mnarigon/backplane/backplane.kicad_sch

## KiCad design backplane.kicad_sch (2023-11-16)

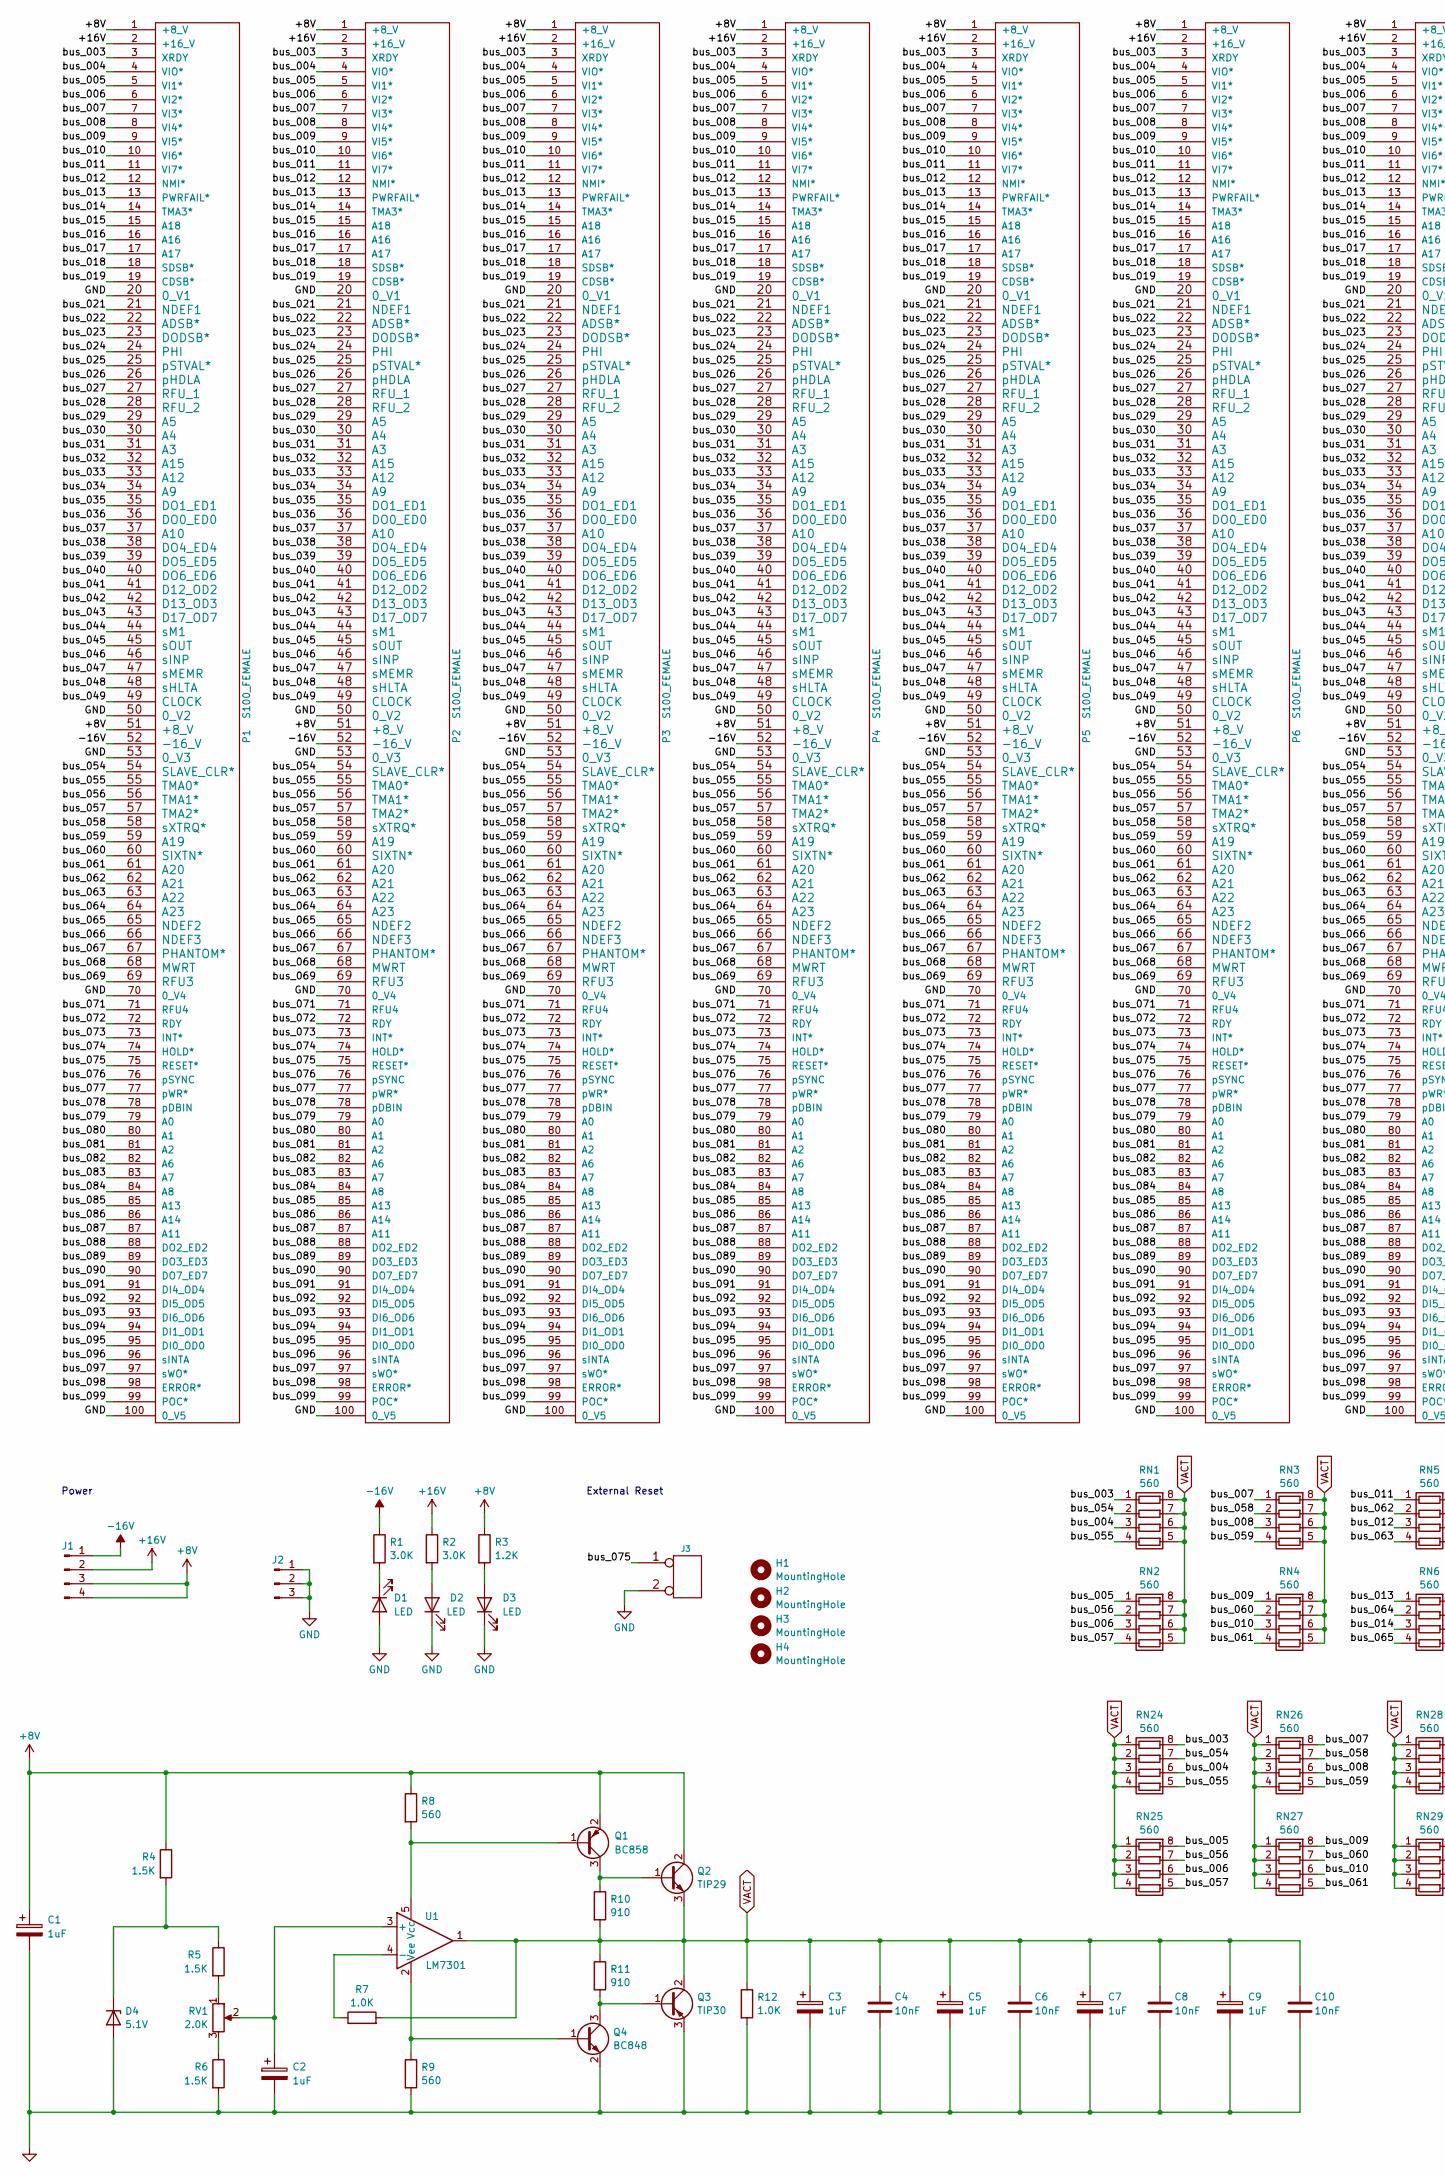
[picture p17: schematic backplane.kicad_sch, part in row 1, column 1]

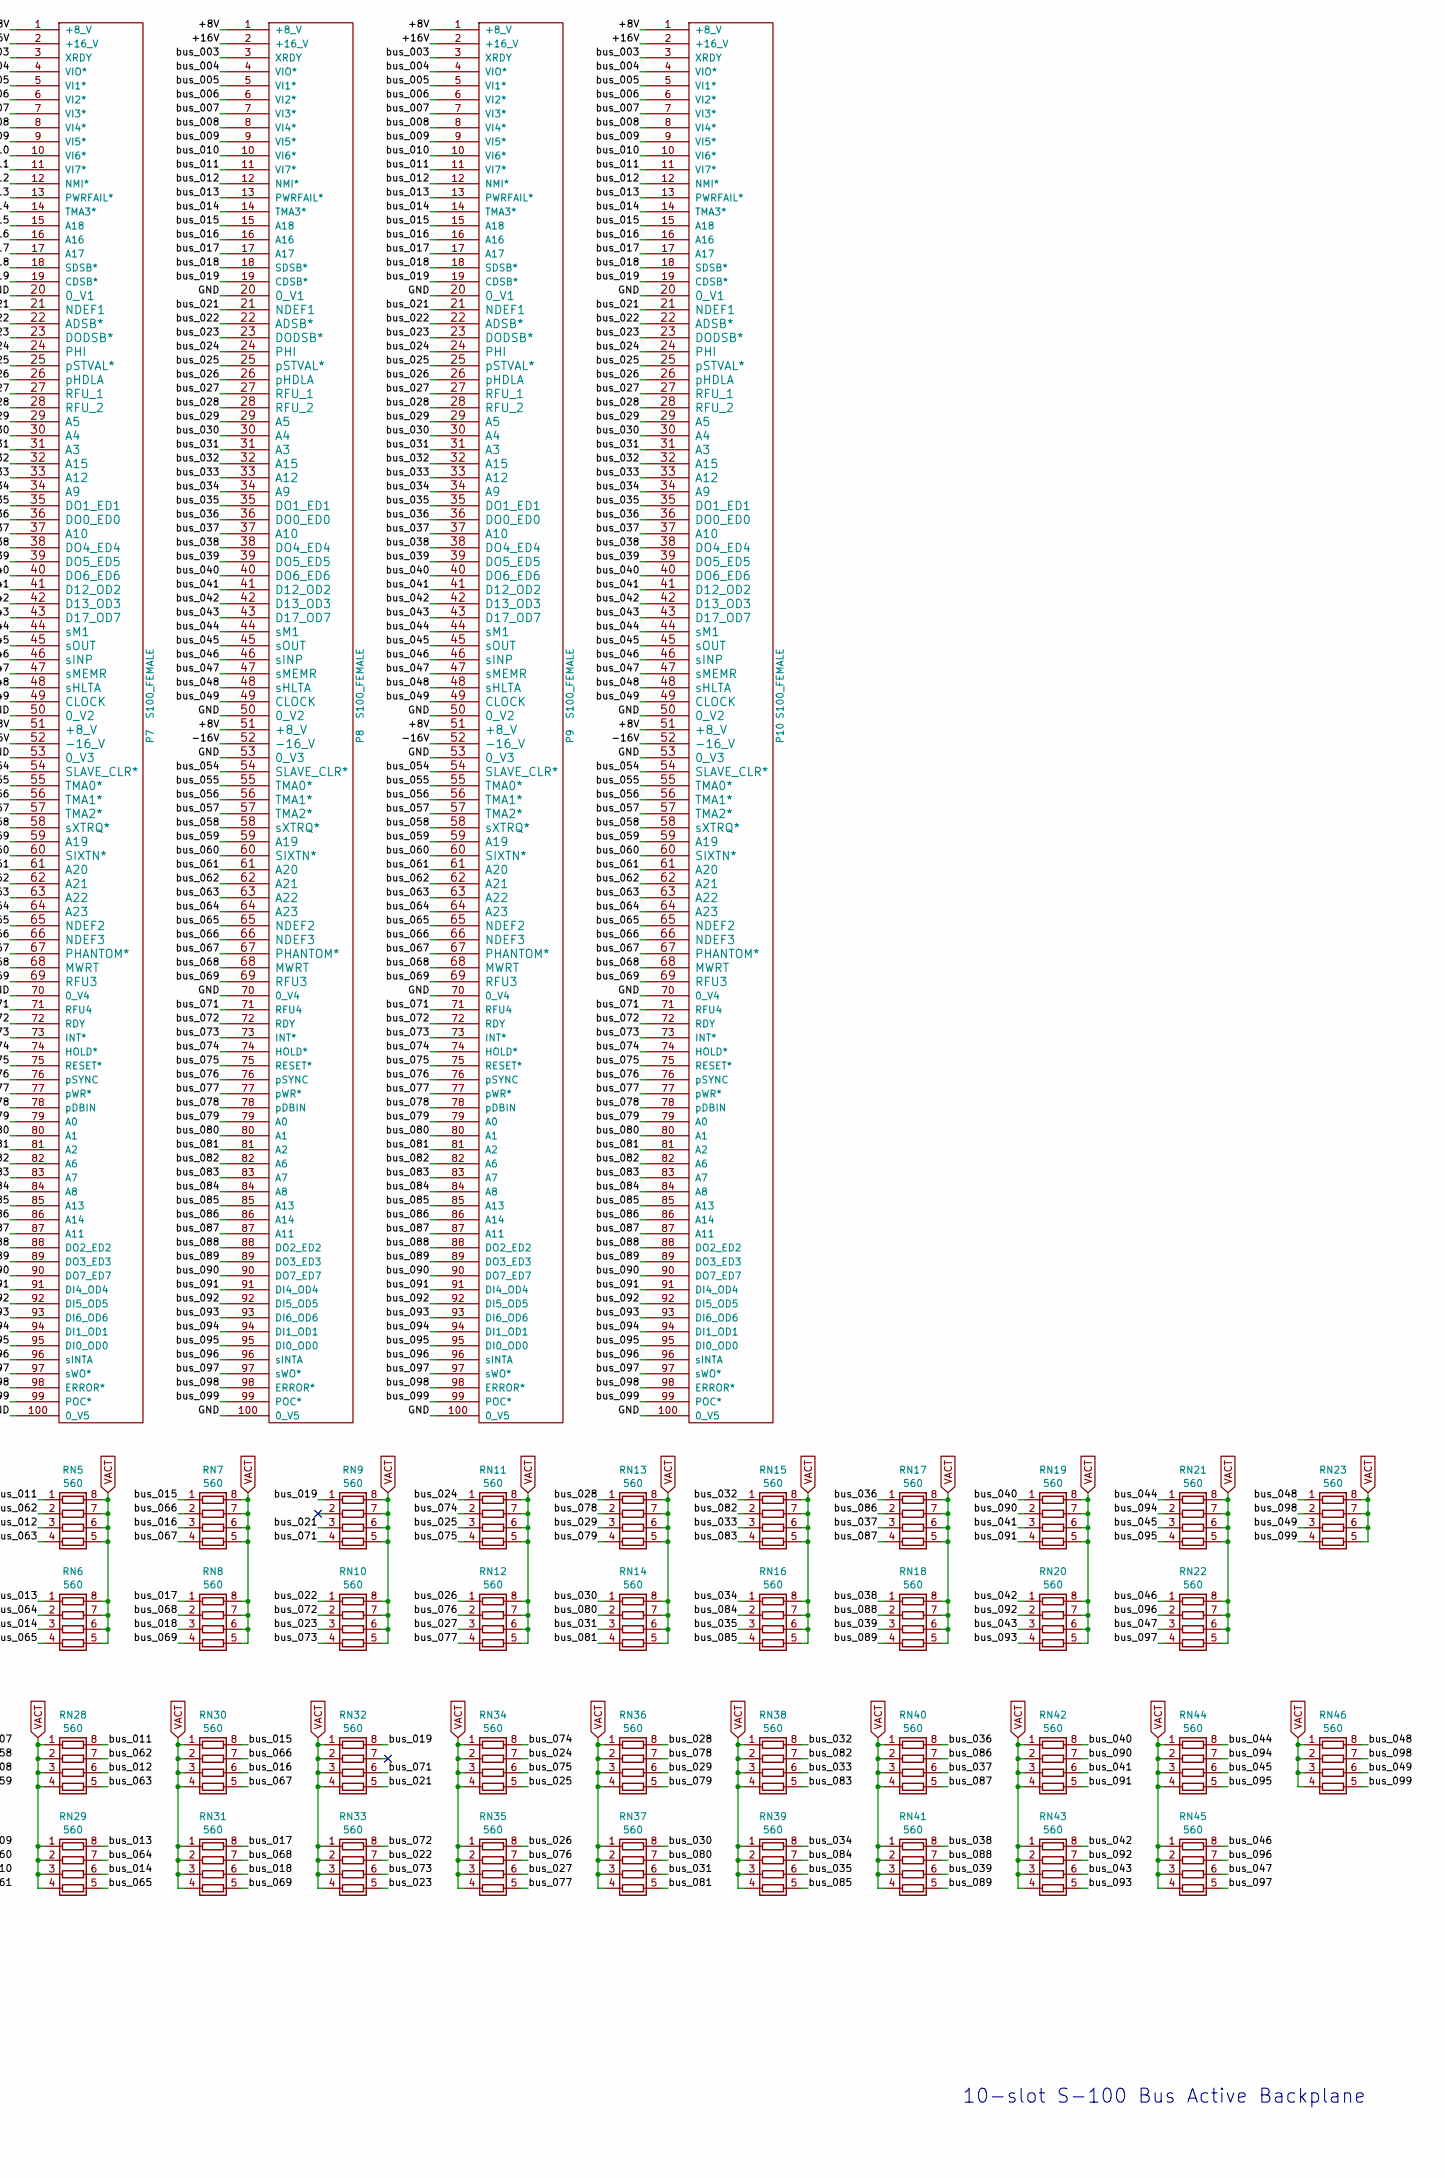
[picture p18: schematic backplane.kicad_sch, part in row 1, column 2]

Parts:
C1, C2, C3, C5, C7, C9: 1uF; CP_0805
C4, C6, C8, C10: 10nF; C_0805
D1, D2, D3: LED; LED_0805
D4: 5.1V; D_SOD-323
H1, H2, H3, H4: MountingHole; Mounting_Hole_6-32
J1: AMP_640445-4
J2: AMP_640445-3
J3: CONN_2; AMP_640454-2
P1, P2, P3, P4, P5, P6, P7, P8, P9, P10: S100_FEMALE; EDAC_346-100-520-202
Q1: BC858; SOT-23-3
Q2: TIP29; TO-220-3_Horizontal
Q3: TIP30; TO-220-3_Horizontal
Q4: BC848; SOT-23-3
R1, R2: 3.0K; R_0805
R3: 1.2K; R_0805
R4, R5, R6: 1.5K; R_0805
R7, R12: 1.0K; R_0805
R8, R9: 560; R_0805
R10, R11: 910; R_0805
RN1, RN2, RN3, RN4, RN5, RN6, RN7, RN8, RN9, RN10, RN11, RN12, RN13, RN14, RN15, RN16, RN17, RN18, RN19, RN20, RN21, RN22, RN23, RN24, RN25, RN26, RN27, RN28, RN29, RN30, RN31, RN32, RN33, RN34, RN35, RN36, RN37, RN38, RN39, RN40, RN41, RN42, RN43, RN44, RN45, RN46: 560; R_Array_Convex_4x1206
RV1: 2.0K; Potentiometer_Bourns_TC33X
U1: LM7301; SOT-23-5

Connections:
+8V: C1.1, J1.3, J1.4, P1.1 (+8_V), P1.51 (+8_V), P2.1 (+8_V), P2.51 (+8_V), P3.1 (+8_V), P3.51 (+8_V), P4.1 (+8_V), P4.51 (+8_V), P5.1 (+8_V), P5.51 (+8_V), P6.1 (+8_V), P6.51 (+8_V), P7.1 (+8_V), P7.51 (+8_V), P8.1 (+8_V), P8.51 (+8_V), P9.1 (+8_V), P9.51 (+8_V), P10.1 (+8_V), P10.51 (+8_V), Q1.2 (E), Q2.2 (C), R3.1, R4.1, R8.1
+16V: J1.2, P1.2 (+16_V), P2.2 (+16_V), P3.2 (+16_V), P4.2 (+16_V), P5.2 (+16_V), P6.2 (+16_V), P7.2 (+16_V), P8.2 (+16_V), P9.2 (+16_V), P10.2 (+16_V), R2.1
-16V: J1.1, P1.52 (-16_V), P2.52 (-16_V), P3.52 (-16_V), P4.52 (-16_V), P5.52 (-16_V), P6.52 (-16_V), P7.52 (-16_V), P8.52 (-16_V), P9.52 (-16_V), P10.52 (-16_V), R1.1
GND: C1.2, C2.2, C3.2, C4.2, C5.2, C6.2, C7.2, C8.2, C9.2, C10.2, D1.2 (A), D2.1 (K), D3.1 (K), D4.2 (A), J2.1, J2.2, J2.3, J3.2 (PM), P1.20 (0_V1), P1.50 (0_V2), P1.53 (0_V3), P1.70 (0_V4), P1.100 (0_V5), P2.20 (0_V1), P2.50 (0_V2), P2.53 (0_V3), P2.70 (0_V4), P2.100 (0_V5), P3.20 (0_V1), P3.50 (0_V2), P3.53 (0_V3), P3.70 (0_V4), P3.100 (0_V5), P4.20 (0_V1), P4.50 (0_V2), P4.53 (0_V3), P4.70 (0_V4), P4.100 (0_V5), P5.20 (0_V1), P5.50 (0_V2), P5.53 (0_V3), P5.70 (0_V4), P5.100 (0_V5), P6.20 (0_V1), P6.50 (0_V2), P6.53 (0_V3), P6.70 (0_V4), P6.100 (0_V5), P7.20 (0_V1), P7.50 (0_V2), P7.53 (0_V3), P7.70 (0_V4), P7.100 (0_V5), P8.20 (0_V1), P8.50 (0_V2), P8.53 (0_V3), P8.70 (0_V4), P8.100 (0_V5), P9.20 (0_V1), P9.50 (0_V2), P9.53 (0_V3), P9.70 (0_V4), P9.100 (0_V5), P10.20 (0_V1), P10.50 (0_V2), P10.53 (0_V3), P10.70 (0_V4), P10.100 (0_V5), Q3.3 (E), Q4.2 (E), R6.2, R9.2, R12.2
unnamed: C2.1, RV1.2, U1.3 (+)
unnamed: D1.1 (K), R1.2
unnamed: D2.2 (A), R2.2
unnamed: D3.2 (A), R3.2
unnamed: D4.1 (K), R4.2, R5.1
unnamed: Q1.1 (B), R8.2, U1.5 (Vcc)
unnamed: Q1.3 (C), Q2.1 (B), R10.1
unnamed: Q3.1 (B), Q4.3 (C), R11.2
unnamed: Q4.1 (B), R9.1, U1.2 (Vee)
unnamed: R5.2, RV1.1
unnamed: R6.1, RV1.3
unnamed: R7.1, U1.4 (-)
VACT: C3.1, C4.1, C5.1, C6.1, C7.1, C8.1, C9.1, C10.1, Q2.3 (E), Q3.2 (C), R7.2, R10.2, R11.1, R12.1, RN1.5 (R4.2), RN1.6 (R3.2), RN1.7 (R2.2), RN1.8 (R1.2), RN2.5 (R4.2), RN2.6 (R3.2), RN2.7 (R2.2), RN2.8 (R1.2), RN3.5 (R4.2), RN3.6 (R3.2), RN3.7 (R2.2), RN3.8 (R1.2), RN4.5 (R4.2), RN4.6 (R3.2), RN4.7 (R2.2), RN4.8 (R1.2), RN5.5 (R4.2), RN5.6 (R3.2), RN5.7 (R2.2), RN5.8 (R1.2), RN6.5 (R4.2), RN6.6 (R3.2), RN6.7 (R2.2), RN6.8 (R1.2), RN7.5 (R4.2), RN7.6 (R3.2), RN7.7 (R2.2), RN7.8 (R1.2), RN8.5 (R4.2), RN8.6 (R3.2), RN8.7 (R2.2), RN8.8 (R1.2), RN9.5 (R4.2), RN9.6 (R3.2), RN9.7 (R2.2), RN9.8 (R1.2), RN10.5 (R4.2), RN10.6 (R3.2), RN10.7 (R2.2), RN10.8 (R1.2), RN11.5 (R4.2), RN11.6 (R3.2), RN11.7 (R2.2), RN11.8 (R1.2), RN12.5 (R4.2), RN12.6 (R3.2), RN12.7 (R2.2), RN12.8 (R1.2), RN13.5 (R4.2), RN13.6 (R3.2), RN13.7 (R2.2), RN13.8 (R1.2), RN14.5 (R4.2), RN14.6 (R3.2), RN14.7 (R2.2), RN14.8 (R1.2), RN15.5 (R4.2), RN15.6 (R3.2), RN15.7 (R2.2), RN15.8 (R1.2), RN16.5 (R4.2), RN16.6 (R3.2), RN16.7 (R2.2), RN16.8 (R1.2), RN17.5 (R4.2), RN17.6 (R3.2), RN17.7 (R2.2), RN17.8 (R1.2), RN18.5 (R4.2), RN18.6 (R3.2), RN18.7 (R2.2), RN18.8 (R1.2), RN19.5 (R4.2), RN19.6 (R3.2), RN19.7 (R2.2), RN19.8 (R1.2), RN20.5 (R4.2), RN20.6 (R3.2), RN20.7 (R2.2), RN20.8 (R1.2), RN21.5 (R4.2), RN21.6 (R3.2), RN21.7 (R2.2), RN21.8 (R1.2), RN22.5 (R4.2), RN22.6 (R3.2), RN22.7 (R2.2), RN22.8 (R1.2), RN23.5 (R4.2), RN23.6 (R3.2), RN23.7 (R2.2), RN23.8 (R1.2), RN24.1 (R1.1), RN24.2 (R2.1), RN24.3 (R3.1), RN24.4 (R4.1), RN25.1 (R1.1), RN25.2 (R2.1), RN25.3 (R3.1), RN25.4 (R4.1), RN26.1 (R1.1), RN26.2 (R2.1), RN26.3 (R3.1), RN26.4 (R4.1), RN27.1 (R1.1), RN27.2 (R2.1), RN27.3 (R3.1), RN27.4 (R4.1), RN28.1 (R1.1), RN28.2 (R2.1), RN28.3 (R3.1), RN28.4 (R4.1), RN29.1 (R1.1), RN29.2 (R2.1), RN29.3 (R3.1), RN29.4 (R4.1), RN30.1 (R1.1), RN30.2 (R2.1), RN30.3 (R3.1), RN30.4 (R4.1), RN31.1 (R1.1), RN31.2 (R2.1), RN31.3 (R3.1), RN31.4 (R4.1), RN32.1 (R1.1), RN32.2 (R2.1), RN32.3 (R3.1), RN32.4 (R4.1), RN33.1 (R1.1), RN33.2 (R2.1), RN33.3 (R3.1), RN33.4 (R4.1), RN34.1 (R1.1), RN34.2 (R2.1), RN34.3 (R3.1), RN34.4 (R4.1), RN35.1 (R1.1), RN35.2 (R2.1), RN35.3 (R3.1), RN35.4 (R4.1), RN36.1 (R1.1), RN36.2 (R2.1), RN36.3 (R3.1), RN36.4 (R4.1), RN37.1 (R1.1), RN37.2 (R2.1), RN37.3 (R3.1), RN37.4 (R4.1), RN38.1 (R1.1), RN38.2 (R2.1), RN38.3 (R3.1), RN38.4 (R4.1), RN39.1 (R1.1), RN39.2 (R2.1), RN39.3 (R3.1), RN39.4 (R4.1), RN40.1 (R1.1), RN40.2 (R2.1), RN40.3 (R3.1), RN40.4 (R4.1), RN41.1 (R1.1), RN41.2 (R2.1), RN41.3 (R3.1), RN41.4 (R4.1), RN42.1 (R1.1), RN42.2 (R2.1), RN42.3 (R3.1), RN42.4 (R4.1), RN43.1 (R1.1), RN43.2 (R2.1), RN43.3 (R3.1), RN43.4 (R4.1), RN44.1 (R1.1), RN44.2 (R2.1), RN44.3 (R3.1), RN44.4 (R4.1), RN45.1 (R1.1), RN45.2 (R2.1), RN45.3 (R3.1), RN45.4 (R4.1), RN46.1 (R1.1), RN46.2 (R2.1), RN46.3 (R3.1), RN46.4 (R4.1), U1.1
bus_003: P1.3 (XRDY), P2.3 (XRDY), P3.3 (XRDY), P4.3 (XRDY), P5.3 (XRDY), P6.3 (XRDY), P7.3 (XRDY), P8.3 (XRDY), P9.3 (XRDY), P10.3 (XRDY), RN1.1 (R1.1), RN24.8 (R1.2)
bus_004: P1.4 (VIO*), P2.4 (VIO*), P3.4 (VIO*), P4.4 (VIO*), P5.4 (VIO*), P6.4 (VIO*), P7.4 (VIO*), P8.4 (VIO*), P9.4 (VIO*), P10.4 (VIO*), RN1.3 (R3.1), RN24.6 (R3.2)
bus_005: P1.5 (VI1*), P2.5 (VI1*), P3.5 (VI1*), P4.5 (VI1*), P5.5 (VI1*), P6.5 (VI1*), P7.5 (VI1*), P8.5 (VI1*), P9.5 (VI1*), P10.5 (VI1*), RN2.1 (R1.1), RN25.8 (R1.2)
bus_006: P1.6 (VI2*), P2.6 (VI2*), P3.6 (VI2*), P4.6 (VI2*), P5.6 (VI2*), P6.6 (VI2*), P7.6 (VI2*), P8.6 (VI2*), P9.6 (VI2*), P10.6 (VI2*), RN2.3 (R3.1), RN25.6 (R3.2)
bus_007: P1.7 (VI3*), P2.7 (VI3*), P3.7 (VI3*), P4.7 (VI3*), P5.7 (VI3*), P6.7 (VI3*), P7.7 (VI3*), P8.7 (VI3*), P9.7 (VI3*), P10.7 (VI3*), RN3.1 (R1.1), RN26.8 (R1.2)
bus_008: P1.8 (VI4*), P2.8 (VI4*), P3.8 (VI4*), P4.8 (VI4*), P5.8 (VI4*), P6.8 (VI4*), P7.8 (VI4*), P8.8 (VI4*), P9.8 (VI4*), P10.8 (VI4*), RN3.3 (R3.1), RN26.6 (R3.2)
bus_009: P1.9 (VI5*), P2.9 (VI5*), P3.9 (VI5*), P4.9 (VI5*), P5.9 (VI5*), P6.9 (VI5*), P7.9 (VI5*), P8.9 (VI5*), P9.9 (VI5*), P10.9 (VI5*), RN4.1 (R1.1), RN27.8 (R1.2)
bus_010: P1.10 (VI6*), P2.10 (VI6*), P3.10 (VI6*), P4.10 (VI6*), P5.10 (VI6*), P6.10 (VI6*), P7.10 (VI6*), P8.10 (VI6*), P9.10 (VI6*), P10.10 (VI6*), RN4.3 (R3.1), RN27.6 (R3.2)
bus_011: P1.11 (VI7*), P2.11 (VI7*), P3.11 (VI7*), P4.11 (VI7*), P5.11 (VI7*), P6.11 (VI7*), P7.11 (VI7*), P8.11 (VI7*), P9.11 (VI7*), P10.11 (VI7*), RN5.1 (R1.1), RN28.8 (R1.2)
bus_012: P1.12 (NMI*), P2.12 (NMI*), P3.12 (NMI*), P4.12 (NMI*), P5.12 (NMI*), P6.12 (NMI*), P7.12 (NMI*), P8.12 (NMI*), P9.12 (NMI*), P10.12 (NMI*), RN5.3 (R3.1), RN28.6 (R3.2)
bus_013: P1.13 (PWRFAIL*), P2.13 (PWRFAIL*), P3.13 (PWRFAIL*), P4.13 (PWRFAIL*), P5.13 (PWRFAIL*), P6.13 (PWRFAIL*), P7.13 (PWRFAIL*), P8.13 (PWRFAIL*), P9.13 (PWRFAIL*), P10.13 (PWRFAIL*), RN6.1 (R1.1), RN29.8 (R1.2)
bus_014: P1.14 (TMA3*), P2.14 (TMA3*), P3.14 (TMA3*), P4.14 (TMA3*), P5.14 (TMA3*), P6.14 (TMA3*), P7.14 (TMA3*), P8.14 (TMA3*), P9.14 (TMA3*), P10.14 (TMA3*), RN6.3 (R3.1), RN29.6 (R3.2)
bus_015: P1.15 (A18), P2.15 (A18), P3.15 (A18), P4.15 (A18), P5.15 (A18), P6.15 (A18), P7.15 (A18), P8.15 (A18), P9.15 (A18), P10.15 (A18), RN7.1 (R1.1), RN30.8 (R1.2)
bus_016: P1.16 (A16), P2.16 (A16), P3.16 (A16), P4.16 (A16), P5.16 (A16), P6.16 (A16), P7.16 (A16), P8.16 (A16), P9.16 (A16), P10.16 (A16), RN7.3 (R3.1), RN30.6 (R3.2)
bus_017: P1.17 (A17), P2.17 (A17), P3.17 (A17), P4.17 (A17), P5.17 (A17), P6.17 (A17), P7.17 (A17), P8.17 (A17), P9.17 (A17), P10.17 (A17), RN8.1 (R1.1), RN31.8 (R1.2)
bus_018: P1.18 (SDSB*), P2.18 (SDSB*), P3.18 (SDSB*), P4.18 (SDSB*), P5.18 (SDSB*), P6.18 (SDSB*), P7.18 (SDSB*), P8.18 (SDSB*), P9.18 (SDSB*), P10.18 (SDSB*), RN8.3 (R3.1), RN31.6 (R3.2)
bus_019: P1.19 (CDSB*), P2.19 (CDSB*), P3.19 (CDSB*), P4.19 (CDSB*), P5.19 (CDSB*), P6.19 (CDSB*), P7.19 (CDSB*), P8.19 (CDSB*), P9.19 (CDSB*), P10.19 (CDSB*), RN9.1 (R1.1), RN32.8 (R1.2)
bus_021: P1.21 (NDEF1), P2.21 (NDEF1), P3.21 (NDEF1), P4.21 (NDEF1), P5.21 (NDEF1), P6.21 (NDEF1), P7.21 (NDEF1), P8.21 (NDEF1), P9.21 (NDEF1), P10.21 (NDEF1), RN9.3 (R3.1), RN32.5 (R4.2)
bus_022: P1.22 (ADSB*), P2.22 (ADSB*), P3.22 (ADSB*), P4.22 (ADSB*), P5.22 (ADSB*), P6.22 (ADSB*), P7.22 (ADSB*), P8.22 (ADSB*), P9.22 (ADSB*), P10.22 (ADSB*), RN10.1 (R1.1), RN33.7 (R2.2)
bus_023: P1.23 (DODSB*), P2.23 (DODSB*), P3.23 (DODSB*), P4.23 (DODSB*), P5.23 (DODSB*), P6.23 (DODSB*), P7.23 (DODSB*), P8.23 (DODSB*), P9.23 (DODSB*), P10.23 (DODSB*), RN10.3 (R3.1), RN33.5 (R4.2)
bus_024: P1.24 (PHI), P2.24 (PHI), P3.24 (PHI), P4.24 (PHI), P5.24 (PHI), P6.24 (PHI), P7.24 (PHI), P8.24 (PHI), P9.24 (PHI), P10.24 (PHI), RN11.1 (R1.1), RN34.7 (R2.2)
bus_025: P1.25 (pSTVAL*), P2.25 (pSTVAL*), P3.25 (pSTVAL*), P4.25 (pSTVAL*), P5.25 (pSTVAL*), P6.25 (pSTVAL*), P7.25 (pSTVAL*), P8.25 (pSTVAL*), P9.25 (pSTVAL*), P10.25 (pSTVAL*), RN11.3 (R3.1), RN34.5 (R4.2)
bus_026: P1.26 (pHDLA), P2.26 (pHDLA), P3.26 (pHDLA), P4.26 (pHDLA), P5.26 (pHDLA), P6.26 (pHDLA), P7.26 (pHDLA), P8.26 (pHDLA), P9.26 (pHDLA), P10.26 (pHDLA), RN12.1 (R1.1), RN35.8 (R1.2)
bus_027: P1.27 (RFU_1), P2.27 (RFU_1), P3.27 (RFU_1), P4.27 (RFU_1), P5.27 (RFU_1), P6.27 (RFU_1), P7.27 (RFU_1), P8.27 (RFU_1), P9.27 (RFU_1), P10.27 (RFU_1), RN12.3 (R3.1), RN35.6 (R3.2)
bus_028: P1.28 (RFU_2), P2.28 (RFU_2), P3.28 (RFU_2), P4.28 (RFU_2), P5.28 (RFU_2), P6.28 (RFU_2), P7.28 (RFU_2), P8.28 (RFU_2), P9.28 (RFU_2), P10.28 (RFU_2), RN13.1 (R1.1), RN36.8 (R1.2)
bus_029: P1.29 (A5), P2.29 (A5), P3.29 (A5), P4.29 (A5), P5.29 (A5), P6.29 (A5), P7.29 (A5), P8.29 (A5), P9.29 (A5), P10.29 (A5), RN13.3 (R3.1), RN36.6 (R3.2)
bus_030: P1.30 (A4), P2.30 (A4), P3.30 (A4), P4.30 (A4), P5.30 (A4), P6.30 (A4), P7.30 (A4), P8.30 (A4), P9.30 (A4), P10.30 (A4), RN14.1 (R1.1), RN37.8 (R1.2)
bus_031: P1.31 (A3), P2.31 (A3), P3.31 (A3), P4.31 (A3), P5.31 (A3), P6.31 (A3), P7.31 (A3), P8.31 (A3), P9.31 (A3), P10.31 (A3), RN14.3 (R3.1), RN37.6 (R3.2)
bus_032: P1.32 (A15), P2.32 (A15), P3.32 (A15), P4.32 (A15), P5.32 (A15), P6.32 (A15), P7.32 (A15), P8.32 (A15), P9.32 (A15), P10.32 (A15), RN15.1 (R1.1), RN38.8 (R1.2)
bus_033: P1.33 (A12), P2.33 (A12), P3.33 (A12), P4.33 (A12), P5.33 (A12), P6.33 (A12), P7.33 (A12), P8.33 (A12), P9.33 (A12), P10.33 (A12), RN15.3 (R3.1), RN38.6 (R3.2)
bus_034: P1.34 (A9), P2.34 (A9), P3.34 (A9), P4.34 (A9), P5.34 (A9), P6.34 (A9), P7.34 (A9), P8.34 (A9), P9.34 (A9), P10.34 (A9), RN16.1 (R1.1), RN39.8 (R1.2)
bus_035: P1.35 (DO1_ED1), P2.35 (DO1_ED1), P3.35 (DO1_ED1), P4.35 (DO1_ED1), P5.35 (DO1_ED1), P6.35 (DO1_ED1), P7.35 (DO1_ED1), P8.35 (DO1_ED1), P9.35 (DO1_ED1), P10.35 (DO1_ED1), RN16.3 (R3.1), RN39.6 (R3.2)
bus_036: P1.36 (DO0_ED0), P2.36 (DO0_ED0), P3.36 (DO0_ED0), P4.36 (DO0_ED0), P5.36 (DO0_ED0), P6.36 (DO0_ED0), P7.36 (DO0_ED0), P8.36 (DO0_ED0), P9.36 (DO0_ED0), P10.36 (DO0_ED0), RN17.1 (R1.1), RN40.8 (R1.2)
bus_037: P1.37 (A10), P2.37 (A10), P3.37 (A10), P4.37 (A10), P5.37 (A10), P6.37 (A10), P7.37 (A10), P8.37 (A10), P9.37 (A10), P10.37 (A10), RN17.3 (R3.1), RN40.6 (R3.2)
bus_038: P1.38 (DO4_ED4), P2.38 (DO4_ED4), P3.38 (DO4_ED4), P4.38 (DO4_ED4), P5.38 (DO4_ED4), P6.38 (DO4_ED4), P7.38 (DO4_ED4), P8.38 (DO4_ED4), P9.38 (DO4_ED4), P10.38 (DO4_ED4), RN18.1 (R1.1), RN41.8 (R1.2)
bus_039: P1.39 (DO5_ED5), P2.39 (DO5_ED5), P3.39 (DO5_ED5), P4.39 (DO5_ED5), P5.39 (DO5_ED5), P6.39 (DO5_ED5), P7.39 (DO5_ED5), P8.39 (DO5_ED5), P9.39 (DO5_ED5), P10.39 (DO5_ED5), RN18.3 (R3.1), RN41.6 (R3.2)
bus_040: P1.40 (DO6_ED6), P2.40 (DO6_ED6), P3.40 (DO6_ED6), P4.40 (DO6_ED6), P5.40 (DO6_ED6), P6.40 (DO6_ED6), P7.40 (DO6_ED6), P8.40 (DO6_ED6), P9.40 (DO6_ED6), P10.40 (DO6_ED6), RN19.1 (R1.1), RN42.8 (R1.2)
bus_041: P1.41 (D12_OD2), P2.41 (D12_OD2), P3.41 (D12_OD2), P4.41 (D12_OD2), P5.41 (D12_OD2), P6.41 (D12_OD2), P7.41 (D12_OD2), P8.41 (D12_OD2), P9.41 (D12_OD2), P10.41 (D12_OD2), RN19.3 (R3.1), RN42.6 (R3.2)
bus_042: P1.42 (D13_OD3), P2.42 (D13_OD3), P3.42 (D13_OD3), P4.42 (D13_OD3), P5.42 (D13_OD3), P6.42 (D13_OD3), P7.42 (D13_OD3), P8.42 (D13_OD3), P9.42 (D13_OD3), P10.42 (D13_OD3), RN20.1 (R1.1), RN43.8 (R1.2)
bus_043: P1.43 (D17_OD7), P2.43 (D17_OD7), P3.43 (D17_OD7), P4.43 (D17_OD7), P5.43 (D17_OD7), P6.43 (D17_OD7), P7.43 (D17_OD7), P8.43 (D17_OD7), P9.43 (D17_OD7), P10.43 (D17_OD7), RN20.3 (R3.1), RN43.6 (R3.2)
bus_044: P1.44 (sM1), P2.44 (sM1), P3.44 (sM1), P4.44 (sM1), P5.44 (sM1), P6.44 (sM1), P7.44 (sM1), P8.44 (sM1), P9.44 (sM1), P10.44 (sM1), RN21.1 (R1.1), RN44.8 (R1.2)
bus_045: P1.45 (sOUT), P2.45 (sOUT), P3.45 (sOUT), P4.45 (sOUT), P5.45 (sOUT), P6.45 (sOUT), P7.45 (sOUT), P8.45 (sOUT), P9.45 (sOUT), P10.45 (sOUT), RN21.3 (R3.1), RN44.6 (R3.2)
bus_046: P1.46 (sINP), P2.46 (sINP), P3.46 (sINP), P4.46 (sINP), P5.46 (sINP), P6.46 (sINP), P7.46 (sINP), P8.46 (sINP), P9.46 (sINP), P10.46 (sINP), RN22.1 (R1.1), RN45.8 (R1.2)
bus_047: P1.47 (sMEMR), P2.47 (sMEMR), P3.47 (sMEMR), P4.47 (sMEMR), P5.47 (sMEMR), P6.47 (sMEMR), P7.47 (sMEMR), P8.47 (sMEMR), P9.47 (sMEMR), P10.47 (sMEMR), RN22.3 (R3.1), RN45.6 (R3.2)
bus_048: P1.48 (sHLTA), P2.48 (sHLTA), P3.48 (sHLTA), P4.48 (sHLTA), P5.48 (sHLTA), P6.48 (sHLTA), P7.48 (sHLTA), P8.48 (sHLTA), P9.48 (sHLTA), P10.48 (sHLTA), RN23.1 (R1.1), RN46.8 (R1.2)
bus_049: P1.49 (CLOCK), P2.49 (CLOCK), P3.49 (CLOCK), P4.49 (CLOCK), P5.49 (CLOCK), P6.49 (CLOCK), P7.49 (CLOCK), P8.49 (CLOCK), P9.49 (CLOCK), P10.49 (CLOCK), RN23.3 (R3.1), RN46.6 (R3.2)
bus_054: P1.54 (SLAVE_CLR*), P2.54 (SLAVE_CLR*), P3.54 (SLAVE_CLR*), P4.54 (SLAVE_CLR*), P5.54 (SLAVE_CLR*), P6.54 (SLAVE_CLR*), P7.54 (SLAVE_CLR*), P8.54 (SLAVE_CLR*), P9.54 (SLAVE_CLR*), P10.54 (SLAVE_CLR*), RN1.2 (R2.1), RN24.7 (R2.2)
bus_055: P1.55 (TMA0*), P2.55 (TMA0*), P3.55 (TMA0*), P4.55 (TMA0*), P5.55 (TMA0*), P6.55 (TMA0*), P7.55 (TMA0*), P8.55 (TMA0*), P9.55 (TMA0*), P10.55 (TMA0*), RN1.4 (R4.1), RN24.5 (R4.2)
bus_056: P1.56 (TMA1*), P2.56 (TMA1*), P3.56 (TMA1*), P4.56 (TMA1*), P5.56 (TMA1*), P6.56 (TMA1*), P7.56 (TMA1*), P8.56 (TMA1*), P9.56 (TMA1*), P10.56 (TMA1*), RN2.2 (R2.1), RN25.7 (R2.2)
bus_057: P1.57 (TMA2*), P2.57 (TMA2*), P3.57 (TMA2*), P4.57 (TMA2*), P5.57 (TMA2*), P6.57 (TMA2*), P7.57 (TMA2*), P8.57 (TMA2*), P9.57 (TMA2*), P10.57 (TMA2*), RN2.4 (R4.1), RN25.5 (R4.2)
bus_058: P1.58 (sXTRQ*), P2.58 (sXTRQ*), P3.58 (sXTRQ*), P4.58 (sXTRQ*), P5.58 (sXTRQ*), P6.58 (sXTRQ*), P7.58 (sXTRQ*), P8.58 (sXTRQ*), P9.58 (sXTRQ*), P10.58 (sXTRQ*), RN3.2 (R2.1), RN26.7 (R2.2)
bus_059: P1.59 (A19), P2.59 (A19), P3.59 (A19), P4.59 (A19), P5.59 (A19), P6.59 (A19), P7.59 (A19), P8.59 (A19), P9.59 (A19), P10.59 (A19), RN3.4 (R4.1), RN26.5 (R4.2)
bus_060: P1.60 (SIXTN*), P2.60 (SIXTN*), P3.60 (SIXTN*), P4.60 (SIXTN*), P5.60 (SIXTN*), P6.60 (SIXTN*), P7.60 (SIXTN*), P8.60 (SIXTN*), P9.60 (SIXTN*), P10.60 (SIXTN*), RN4.2 (R2.1), RN27.7 (R2.2)
bus_061: P1.61 (A20), P2.61 (A20), P3.61 (A20), P4.61 (A20), P5.61 (A20), P6.61 (A20), P7.61 (A20), P8.61 (A20), P9.61 (A20), P10.61 (A20), RN4.4 (R4.1), RN27.5 (R4.2)
bus_062: P1.62 (A21), P2.62 (A21), P3.62 (A21), P4.62 (A21), P5.62 (A21), P6.62 (A21), P7.62 (A21), P8.62 (A21), P9.62 (A21), P10.62 (A21), RN5.2 (R2.1), RN28.7 (R2.2)
bus_063: P1.63 (A22), P2.63 (A22), P3.63 (A22), P4.63 (A22), P5.63 (A22), P6.63 (A22), P7.63 (A22), P8.63 (A22), P9.63 (A22), P10.63 (A22), RN5.4 (R4.1), RN28.5 (R4.2)
bus_064: P1.64 (A23), P2.64 (A23), P3.64 (A23), P4.64 (A23), P5.64 (A23), P6.64 (A23), P7.64 (A23), P8.64 (A23), P9.64 (A23), P10.64 (A23), RN6.2 (R2.1), RN29.7 (R2.2)
bus_065: P1.65 (NDEF2), P2.65 (NDEF2), P3.65 (NDEF2), P4.65 (NDEF2), P5.65 (NDEF2), P6.65 (NDEF2), P7.65 (NDEF2), P8.65 (NDEF2), P9.65 (NDEF2), P10.65 (NDEF2), RN6.4 (R4.1), RN29.5 (R4.2)
bus_066: P1.66 (NDEF3), P2.66 (NDEF3), P3.66 (NDEF3), P4.66 (NDEF3), P5.66 (NDEF3), P6.66 (NDEF3), P7.66 (NDEF3), P8.66 (NDEF3), P9.66 (NDEF3), P10.66 (NDEF3), RN7.2 (R2.1), RN30.7 (R2.2)
bus_067: P1.67 (PHANTOM*), P2.67 (PHANTOM*), P3.67 (PHANTOM*), P4.67 (PHANTOM*), P5.67 (PHANTOM*), P6.67 (PHANTOM*), P7.67 (PHANTOM*), P8.67 (PHANTOM*), P9.67 (PHANTOM*), P10.67 (PHANTOM*), RN7.4 (R4.1), RN30.5 (R4.2)
bus_068: P1.68 (MWRT), P2.68 (MWRT), P3.68 (MWRT), P4.68 (MWRT), P5.68 (MWRT), P6.68 (MWRT), P7.68 (MWRT), P8.68 (MWRT), P9.68 (MWRT), P10.68 (MWRT), RN8.2 (R2.1), RN31.7 (R2.2)
bus_069: P1.69 (RFU3), P2.69 (RFU3), P3.69 (RFU3), P4.69 (RFU3), P5.69 (RFU3), P6.69 (RFU3), P7.69 (RFU3), P8.69 (RFU3), P9.69 (RFU3), P10.69 (RFU3), RN8.4 (R4.1), RN31.5 (R4.2)
bus_071: P1.71 (RFU4), P2.71 (RFU4), P3.71 (RFU4), P4.71 (RFU4), P5.71 (RFU4), P6.71 (RFU4), P7.71 (RFU4), P8.71 (RFU4), P9.71 (RFU4), P10.71 (RFU4), RN9.4 (R4.1), RN32.6 (R3.2)
bus_072: P1.72 (RDY), P2.72 (RDY), P3.72 (RDY), P4.72 (RDY), P5.72 (RDY), P6.72 (RDY), P7.72 (RDY), P8.72 (RDY), P9.72 (RDY), P10.72 (RDY), RN10.2 (R2.1), RN33.8 (R1.2)
bus_073: P1.73 (INT*), P2.73 (INT*), P3.73 (INT*), P4.73 (INT*), P5.73 (INT*), P6.73 (INT*), P7.73 (INT*), P8.73 (INT*), P9.73 (INT*), P10.73 (INT*), RN10.4 (R4.1), RN33.6 (R3.2)
bus_074: P1.74 (HOLD*), P2.74 (HOLD*), P3.74 (HOLD*), P4.74 (HOLD*), P5.74 (HOLD*), P6.74 (HOLD*), P7.74 (HOLD*), P8.74 (HOLD*), P9.74 (HOLD*), P10.74 (HOLD*), RN11.2 (R2.1), RN34.8 (R1.2)
bus_075: J3.1, P1.75 (RESET*), P2.75 (RESET*), P3.75 (RESET*), P4.75 (RESET*), P5.75 (RESET*), P6.75 (RESET*), P7.75 (RESET*), P8.75 (RESET*), P9.75 (RESET*), P10.75 (RESET*), RN11.4 (R4.1), RN34.6 (R3.2)
bus_076: P1.76 (pSYNC), P2.76 (pSYNC), P3.76 (pSYNC), P4.76 (pSYNC), P5.76 (pSYNC), P6.76 (pSYNC), P7.76 (pSYNC), P8.76 (pSYNC), P9.76 (pSYNC), P10.76 (pSYNC), RN12.2 (R2.1), RN35.7 (R2.2)
bus_077: P1.77 (pWR*), P2.77 (pWR*), P3.77 (pWR*), P4.77 (pWR*), P5.77 (pWR*), P6.77 (pWR*), P7.77 (pWR*), P8.77 (pWR*), P9.77 (pWR*), P10.77 (pWR*), RN12.4 (R4.1), RN35.5 (R4.2)
bus_078: P1.78 (pDBIN), P2.78 (pDBIN), P3.78 (pDBIN), P4.78 (pDBIN), P5.78 (pDBIN), P6.78 (pDBIN), P7.78 (pDBIN), P8.78 (pDBIN), P9.78 (pDBIN), P10.78 (pDBIN), RN13.2 (R2.1), RN36.7 (R2.2)
bus_079: P1.79 (A0), P2.79 (A0), P3.79 (A0), P4.79 (A0), P5.79 (A0), P6.79 (A0), P7.79 (A0), P8.79 (A0), P9.79 (A0), P10.79 (A0), RN13.4 (R4.1), RN36.5 (R4.2)
bus_080: P1.80 (A1), P2.80 (A1), P3.80 (A1), P4.80 (A1), P5.80 (A1), P6.80 (A1), P7.80 (A1), P8.80 (A1), P9.80 (A1), P10.80 (A1), RN14.2 (R2.1), RN37.7 (R2.2)
bus_081: P1.81 (A2), P2.81 (A2), P3.81 (A2), P4.81 (A2), P5.81 (A2), P6.81 (A2), P7.81 (A2), P8.81 (A2), P9.81 (A2), P10.81 (A2), RN14.4 (R4.1), RN37.5 (R4.2)
bus_082: P1.82 (A6), P2.82 (A6), P3.82 (A6), P4.82 (A6), P5.82 (A6), P6.82 (A6), P7.82 (A6), P8.82 (A6), P9.82 (A6), P10.82 (A6), RN15.2 (R2.1), RN38.7 (R2.2)
bus_083: P1.83 (A7), P2.83 (A7), P3.83 (A7), P4.83 (A7), P5.83 (A7), P6.83 (A7), P7.83 (A7), P8.83 (A7), P9.83 (A7), P10.83 (A7), RN15.4 (R4.1), RN38.5 (R4.2)
bus_084: P1.84 (A8), P2.84 (A8), P3.84 (A8), P4.84 (A8), P5.84 (A8), P6.84 (A8), P7.84 (A8), P8.84 (A8), P9.84 (A8), P10.84 (A8), RN16.2 (R2.1), RN39.7 (R2.2)
bus_085: P1.85 (A13), P2.85 (A13), P3.85 (A13), P4.85 (A13), P5.85 (A13), P6.85 (A13), P7.85 (A13), P8.85 (A13), P9.85 (A13), P10.85 (A13), RN16.4 (R4.1), RN39.5 (R4.2)
bus_086: P1.86 (A14), P2.86 (A14), P3.86 (A14), P4.86 (A14), P5.86 (A14), P6.86 (A14), P7.86 (A14), P8.86 (A14), P9.86 (A14), P10.86 (A14), RN17.2 (R2.1), RN40.7 (R2.2)
bus_087: P1.87 (A11), P2.87 (A11), P3.87 (A11), P4.87 (A11), P5.87 (A11), P6.87 (A11), P7.87 (A11), P8.87 (A11), P9.87 (A11), P10.87 (A11), RN17.4 (R4.1), RN40.5 (R4.2)
bus_088: P1.88 (DO2_ED2), P2.88 (DO2_ED2), P3.88 (DO2_ED2), P4.88 (DO2_ED2), P5.88 (DO2_ED2), P6.88 (DO2_ED2), P7.88 (DO2_ED2), P8.88 (DO2_ED2), P9.88 (DO2_ED2), P10.88 (DO2_ED2), RN18.2 (R2.1), RN41.7 (R2.2)
bus_089: P1.89 (DO3_ED3), P2.89 (DO3_ED3), P3.89 (DO3_ED3), P4.89 (DO3_ED3), P5.89 (DO3_ED3), P6.89 (DO3_ED3), P7.89 (DO3_ED3), P8.89 (DO3_ED3), P9.89 (DO3_ED3), P10.89 (DO3_ED3), RN18.4 (R4.1), RN41.5 (R4.2)
bus_090: P1.90 (DO7_ED7), P2.90 (DO7_ED7), P3.90 (DO7_ED7), P4.90 (DO7_ED7), P5.90 (DO7_ED7), P6.90 (DO7_ED7), P7.90 (DO7_ED7), P8.90 (DO7_ED7), P9.90 (DO7_ED7), P10.90 (DO7_ED7), RN19.2 (R2.1), RN42.7 (R2.2)
bus_091: P1.91 (DI4_OD4), P2.91 (DI4_OD4), P3.91 (DI4_OD4), P4.91 (DI4_OD4), P5.91 (DI4_OD4), P6.91 (DI4_OD4), P7.91 (DI4_OD4), P8.91 (DI4_OD4), P9.91 (DI4_OD4), P10.91 (DI4_OD4), RN19.4 (R4.1), RN42.5 (R4.2)
bus_092: P1.92 (DI5_OD5), P2.92 (DI5_OD5), P3.92 (DI5_OD5), P4.92 (DI5_OD5), P5.92 (DI5_OD5), P6.92 (DI5_OD5), P7.92 (DI5_OD5), P8.92 (DI5_OD5), P9.92 (DI5_OD5), P10.92 (DI5_OD5), RN20.2 (R2.1), RN43.7 (R2.2)
bus_093: P1.93 (DI6_OD6), P2.93 (DI6_OD6), P3.93 (DI6_OD6), P4.93 (DI6_OD6), P5.93 (DI6_OD6), P6.93 (DI6_OD6), P7.93 (DI6_OD6), P8.93 (DI6_OD6), P9.93 (DI6_OD6), P10.93 (DI6_OD6), RN20.4 (R4.1), RN43.5 (R4.2)
bus_094: P1.94 (DI1_OD1), P2.94 (DI1_OD1), P3.94 (DI1_OD1), P4.94 (DI1_OD1), P5.94 (DI1_OD1), P6.94 (DI1_OD1), P7.94 (DI1_OD1), P8.94 (DI1_OD1), P9.94 (DI1_OD1), P10.94 (DI1_OD1), RN21.2 (R2.1), RN44.7 (R2.2)
bus_095: P1.95 (DI0_OD0), P2.95 (DI0_OD0), P3.95 (DI0_OD0), P4.95 (DI0_OD0), P5.95 (DI0_OD0), P6.95 (DI0_OD0), P7.95 (DI0_OD0), P8.95 (DI0_OD0), P9.95 (DI0_OD0), P10.95 (DI0_OD0), RN21.4 (R4.1), RN44.5 (R4.2)
bus_096: P1.96 (sINTA), P2.96 (sINTA), P3.96 (sINTA), P4.96 (sINTA), P5.96 (sINTA), P6.96 (sINTA), P7.96 (sINTA), P8.96 (sINTA), P9.96 (sINTA), P10.96 (sINTA), RN22.2 (R2.1), RN45.7 (R2.2)
bus_097: P1.97 (sWO*), P2.97 (sWO*), P3.97 (sWO*), P4.97 (sWO*), P5.97 (sWO*), P6.97 (sWO*), P7.97 (sWO*), P8.97 (sWO*), P9.97 (sWO*), P10.97 (sWO*), RN22.4 (R4.1), RN45.5 (R4.2)
bus_098: P1.98 (ERROR*), P2.98 (ERROR*), P3.98 (ERROR*), P4.98 (ERROR*), P5.98 (ERROR*), P6.98 (ERROR*), P7.98 (ERROR*), P8.98 (ERROR*), P9.98 (ERROR*), P10.98 (ERROR*), RN23.2 (R2.1), RN46.7 (R2.2)
bus_099: P1.99 (POC*), P2.99 (POC*), P3.99 (POC*), P4.99 (POC*), P5.99 (POC*), P6.99 (POC*), P7.99 (POC*), P8.99 (POC*), P9.99 (POC*), P10.99 (POC*), RN23.4 (R4.1), RN46.5 (R4.2)

Notes on the sheet:
Power
10-slot S-100 Bus Active Backplane
External Reset
